eurovibes/sertest-ng/software/STM32CubeMX/sertest-ng-64pin/sertest-ng-64pin.ioc

Mcu.UserName=STM32G431RBTx
PA0.Signal=USART2_CTS
PA1.Signal=USART2_RTS
PA11.Signal=USB_DM
PA12.Signal=USB_DP
PA13.Signal=SYS_JTMS-SWDIO
PA14.Signal=SYS_JTCK-SWCLK
PA2.Signal=USART2_TX
PA3.Signal=USART2_RX
PA4.GPIO_Label=USART2_DCD
PA4.Signal=GPIO_Output
PA5.GPIO_Label=USART2_DTR
PA5.Signal=GPIO_Input
PA6.GPIO_Label=USART2_DSR
PA6.Signal=GPIO_Output
PA7.GPIO_Label=USART2_RI
PA7.Signal=GPIO_Output
PA8.Signal=I2C2_SDA
PA9.Signal=I2C2_SCL
PB10.Signal=USART3_TX
PB11.Signal=USART3_RX
PB12.GPIO_Label=STB
PB12.Signal=GPIO_Output
PB3.Signal=SYS_JTDO-SWO
PB4.GPIO_Label=LED0
PB4.Signal=GPIO_Output
PB5.GPIO_Label=LED1
PB5.Signal=GPIO_Output
PB6.GPIO_Label=LED2
PB6.Signal=GPIO_Output
PB7.GPIO_Label=LED3
PB7.Signal=GPIO_Output
PB8-BOOT0.Signal=FDCAN1_RX
PB9.Signal=FDCAN1_TX
PC1.GPIO_Label=RS485
PC1.Signal=GPIO_Output
PC10.GPIO_Label=nRE
PC10.Signal=GPIO_Output
PC11.GPIO_Label=nSLEW
PC11.Signal=GPIO_Output
PC12.GPIO_Label=nSD
PC12.Signal=GPIO_Output
PC14-OSC32_IN.Signal=RCC_OSC32_IN
PC15-OSC32_OUT.Signal=RCC_OSC32_OUT
PC2.GPIO_Label=HALF
PC2.Signal=GPIO_Output
PC3.GPIO_Label=nSHDN
PC3.Signal=GPIO_Output
PC4.Signal=USART1_TX
PC5.Signal=USART1_RX
PC6.GPIO_Label=EN
PC6.Signal=GPIO_Output
PF0-OSC_IN.Signal=RCC_OSC_IN
PF1-OSC_OUT.Signal=RCC_OSC_OUT
